kholia/pico-tnc-plus/pcb/pcb.kicad_sch

## KiCad design pcb/pcb.kicad_sch (2024-08-14)

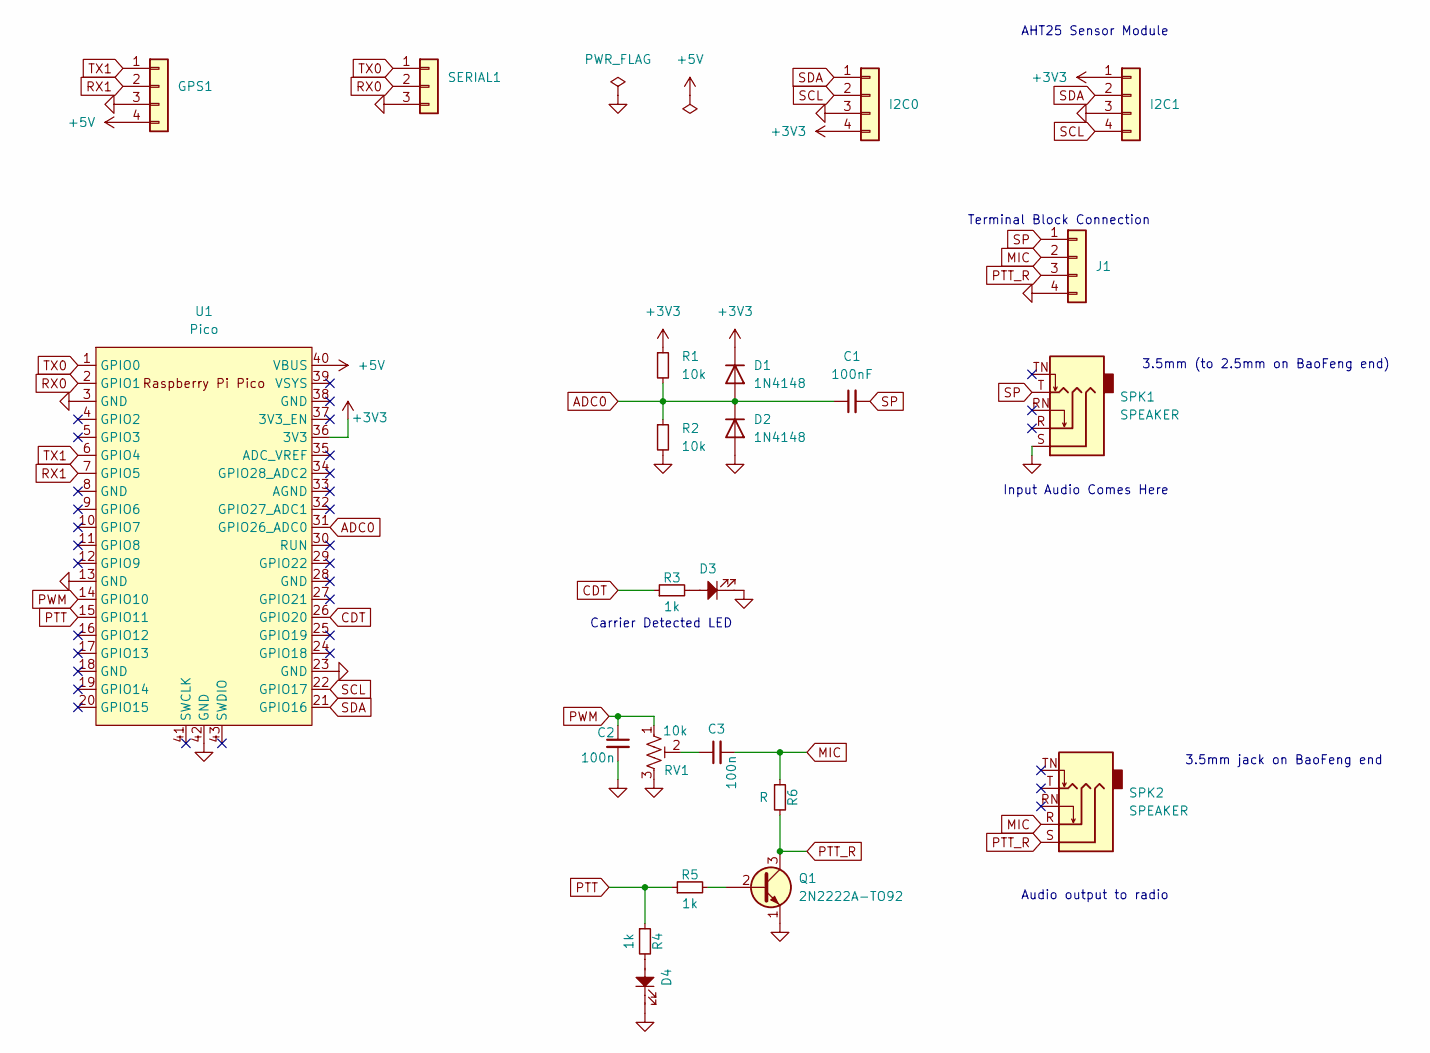
[picture p4: schematic pcb.kicad_sch]

Parts:
C1: 100nF; C_1206_3216Metric_Pad1.33x1.80mm_HandSolder
C2, C3: 100n; C_1206_3216Metric_Pad1.33x1.80mm_HandSolder
D1, D2: 1N4148; D_DO-35_SOD27_P7.62mm_Horizontal
D3, D4: LED_3mm; LED_D3.0mm
GPS1: Conn_01x04; PinHeader_1x04_P2.54mm_Vertical; Part Number 1-0401FBV0T
I2C0: Conn_01x04; PinHeader_1x04_P2.54mm_Vertical; Part Number 1-0401FBV0T
I2C1: Conn_01x04; PinHeader_1x04_P1.27mm_Vertical; Part Number 1-0401FBV0T
J1: Conn_01x04; PinHeader_1x04_P2.54mm_Vertical; Part Number 1-0401FBV0T
Q1: 2N2222A-TO92; TO-92_HandSolder
R1, R2: 10k; R_1206_3216Metric_Pad1.30x1.75mm_HandSolder
R3, R4, R5: 1k; R_1206_3216Metric_Pad1.30x1.75mm_HandSolder
R6: R; R_1206_3216Metric_Pad1.30x1.75mm_HandSolder
RV1: 10k; Potentiometer_Runtron_RM-065_Vertical
SERIAL1: Conn_01x03; PinHeader_1x03_P2.54mm_Vertical; Part Number 1-0301FBV0T
SPK1, SPK2: SPEAKER; PJ-307
U1: Pico; RPi_Pico_SMD_TH

Connections:
+3V3: D1.1 (K), I2C0.4, I2C1.1, R1.1, U1.36 (3V3)
+5V: GPS1.4, U1.40 (VBUS)
ADC0: C1.1, D1.2 (A), D2.1 (K), R1.2, R2.1, U1.31 (GPIO26_ADC0)
CDT: R3.1, U1.26 (GPIO20)
GND: C2.2, D2.2 (A), D3.1, D4.1, GPS1.3, I2C0.3, I2C1.3, J1.4, Q1.1 (E), R2.2, RV1.3, SERIAL1.3, SPK1.S, U1.3 (GND), U1.13 (GND), U1.23 (GND), U1.42 (GND)
MIC: C3.2, J1.2, R6.1, SPK2.R
unnamed: C3.1, RV1.2
unnamed: D3.2, R3.2
unnamed: D4.2, R4.2
unnamed: Q1.2 (B), R5.2
PTT: R4.1, R5.1, U1.15 (GPIO11)
PTT_R: J1.3, Q1.3 (C), R6.2, SPK2.S
PWM: C2.1, RV1.1, U1.14 (GPIO10)
RX0: SERIAL1.2, U1.2 (GPIO1)
RX1: GPS1.2, U1.7 (GPIO5)
SCL: I2C0.2, I2C1.4, U1.22 (GPIO17)
SDA: I2C0.1, I2C1.2, U1.21 (GPIO16)
SP: C1.2, J1.1, SPK1.T
TX0: SERIAL1.1, U1.1 (GPIO0)
TX1: GPS1.1, U1.6 (GPIO4)

Notes on the sheet:
Carrier Detected LED
3.5mm (to 2.5mm on BaoFeng end)
AHT25 Sensor Module
Input Audio Comes Here
Audio output to radio
Terminal Block Connection
3.5mm jack on BaoFeng end
